lshw/wifi_disp/wifi_disp/proc3.h

#ifndef __PROC3_H__
#define __PROC3_H__
//发送温度湿度压力到tcp服务器
void proc3_setup() {
  WiFiUDP udp;
  String msg;
  if (nvram.proc3_host[0] == 0)
    return;
  set_hostname();
  if (nvram.have_dht) {
    if (wendu < -299.0)
      dht_();
    wifi_set_opmode(STATION_MODE);
    wifi_station_connect();
  }
  _myTicker.attach(1, timer1s);
  wait_connected(10000);
  nvram.charge = 1;  //充电
  nvram.change = 1;
  save_nvram();
  if (nvram.have_dht) {
    if (wendu < -299.0) {
      if (!dht_()) poweroff(1);
    }
  }
  get_value();
  fix_proc3_set();
  shan();
  Serial.flush();
  if (WiFi_isConnected()) {
    delay(100);
    msg = val_str();
    udp.begin(nvram.proc3_port);
    if (udp.beginPacket(nvram.proc3_host, nvram.proc3_port)
        || udp.beginPacket(nvram.proc3_host, nvram.proc3_port)
        || udp.beginPacket(nvram.proc3_host, nvram.proc3_port)) {
      if (udp.println(msg)
          || udp.println(msg)
          || udp.println(msg)) {
        udp.endPacket();
        Serial.println(F("send ok"));
      }
    }
    Serial.printf_P(PSTR("to %s:%d [%s]\r\n"), nvram.proc3_host, nvram.proc3_port, msg.c_str());
    Serial.flush();
  }
  delay(100);
  poweroff(nvram.proc3_sec);
}
#endif  //__PROC3_H__
