lshw/wifi_disp/wifi_disp/dht22.h

#ifndef __DHT_H__
#define __DHT_H__

extern float wendu, shidu;
uint8_t temp_data[6];
uint32_t dht_next = 600;
#define DHT_PIN 0
bool dht() {
  uint8_t p1, dat[40];
  // empty output data.
  pinMode(DHT_PIN, INPUT_PULLUP);
  if (dht_next > millis()) {
    if (dht_next > millis() + 600)
      dht_next = millis() + 600;
    Serial.printf_P(PSTR("delay(%ld)\r\n"), dht_next - millis());
    while (dht_next > millis()) {
      delay(100);
      yield();
    }
  }
  dht_next = millis() + 600;

  // According to protocol: http://akizukidenshi.com/download/ds/aosong/AM2302.pdf
  // notify DHT22 to start:
  //    1. T(be), PULL LOW 1ms(0.8-20ms).
  //    2. T(go), PULL HIGH 30us(20-200us), use 40us.
  //    3. SET TO INPUT or INPUT_PULLUP.
  pinMode(DHT_PIN, OUTPUT);
  digitalWrite(DHT_PIN, LOW);
  cli();
  delayMicroseconds(20000);
  // Pull high and set to input, before wait 40us.
  // @see https://github.com/winlinvip/SimpleDHT/issues/4
  // @see https://github.com/winlinvip/SimpleDHT/pull/5
  digitalWrite(DHT_PIN, HIGH);
  pinMode(DHT_PIN, INPUT_PULLUP);
  delayMicroseconds(40);

  // DHT22 starting:
  //    1. T(rel), PULL LOW 80us(75-85us).
  //    2. T(reh), PULL HIGH 80us(75-85us).
  //levelTime(pin, LOW);
  //levelTime(pin, HIGH);
  p1 = pulseIn(DHT_PIN, HIGH, 200);
  if (p1 > 120) {
    sei();
    return false;
  }
  // DHT22 data transmite:
  //    1. T(LOW), 1bit start, PULL LOW 50us(48-55us).
  //    2. T(H0), PULL HIGH 26us(22-30us), bit(0)
  //    3. T(H1), PULL HIGH 70us(68-75us), bit(1)
  for (int j = 0; j < 40; j++) {
    dat[j] = pulseIn(DHT_PIN, HIGH, 200);
  }
  sei();
  for (int j = 0; j < 40; j++) {
    temp_data[j / 8] = (temp_data[j / 8] << 1) | (dat[j] > 40 ? 1 : 0);  // specs: 22-30us -> 0, 70us -> 1
  }
  Serial.printf_P(PSTR("start=%d, %02x%02x %02x%02x %02x\r\n"), p1,
                  temp_data[0],
                  temp_data[1],
                  temp_data[2],
                  temp_data[3],
                  temp_data[4]);
  for (int j = 0; j < 40; j++) {
    Serial.printf_P(PSTR(" %02d"), dat[j]);
    if (j % 8 == 7)
      Serial.println();
  }
  if (
    ((temp_data[0] + temp_data[1] + temp_data[2] + temp_data[3]) & 0xff) == temp_data[4]
    && ((temp_data[0] + temp_data[1] + temp_data[2] + temp_data[3] + temp_data[4]) != 0)) {
    wendu = 0.1 * ((temp_data[2] & 0x7f) << 8 | temp_data[3]);
    shidu = 0.1 * (temp_data[0] << 8 | temp_data[1]);
    if ((temp_data[2] & 0x80) != 0)
      wendu = -wendu;
    Serial.printf_P(PSTR("millis()=%ld, 温度=%.1f, 湿度=%.1f%%\r\n"), millis(), wendu, shidu);
    return true;
  } else {
    wendu = -999.0;
    shidu = -999.0;
    Serial.println(F("数据校验错"));
    return false;
  }
}
bool dht_() {
  if (!dht() && !dht() && !dht())
    return dht();
  return true;
}
#endif
