lshw/wifi_disp/wifi_disp/proc4.h

#ifndef __PROC4_H__
#define __PROC4_H__
//lora转发到internet  通过wifi
uint16_t send_limit = 0;
void limit_speed() {  //令牌桶算法，限制转发的速率
  if (send_limit > 0) send_limit--;
}
void proc4_setup() {
  init1();
  if (power_in) {
    _myTicker.attach(1, limit_speed);
    Serial.println(F("lora 网关模式"));
    disp(F("P4-L "));
    wifi_set_opmode(STATION_MODE);
    wifi_station_connect();
    set_hostname();
    hello();
    if (!wait_connected(30000)) {
      poweroff(10);
    }

  } else {
    Serial.println(F("lora 远端模式"));
    disp(F("P4-S "));
    lora_send_wendu();
    delay(100);
    poweroff(nvram.proc3_sec);
  }
}
#endif  //__PROC4_H__
