lshw/wifi_disp/lora_mini/lora.h

#include <SPI.h>
#include "sx1278.h"
#define DIO0 2
#define DIO1 3
#define DIO2 A0
#define NSS_PIN  10
#define RESET_PIN  9
#define LORA_VCC 8
LoRa lora;
extern float temp, bat_v;
extern byte dsn[8];
uint8_t len;
char buf[256];
uint16_t lora_count = 0;
uint32_t ms;
void lora_tx_int() {
  //digitalWrite(13,LOW);
//  Serial.begin(9600);
//  Serial.println(millis() - ms);
//  Serial.flush();
  min_dog = 0;//清看门狗
}
void lora_send_loop() {
  lora_count++;
  String str;
  pinMode(DIO0, INPUT);
  digitalWrite(DIO0, LOW);
  lora.enterTxMode();
  lora.setTxInterrupt();	// enable RxDoneIrq
  sprintf(buf, "S%04d,%02x%02x%02x%02x%02x%02x%02x%02x,", lora_count % 10000, dsn[0], dsn[1], dsn[2], dsn[3], dsn[4], dsn[5], dsn[6], dsn[7], temp, (int)(bat_v * 1000));
  str = String(temp);
  strcat(buf, String(temp).c_str());
  strcat(buf, ",");
  strcat(buf, String(bat_v).c_str());
  Serial.println(buf);
  //disp(disp_buf);
  //digitalWrite(13,HIGH);
  lora.sendPackage((uint8_t *)buf, strlen(buf)); // sending data
  attachInterrupt(0, lora_tx_int, HIGH);
  wdt_reset(); //让wdt中断，1秒后发生，防止wdt中断，干扰lora发送完成中断
  ms = millis();
  power_down();//cpu掉电模式， 等待发送完成
  detachInterrupt(0);
  lora.clearIRQFlags();
  lora.sleep();//发送完成，lora休眠
}
uint8_t lora_rxtx = 0; //1:rx 2:tx
void lora_receive_loop() {
  if (lora_rxtx != 1) {
    lora.rxInit();
    lora_rxtx = 1;
  }
  if (lora.waitIrq()) {
    lora.clearIRQFlags();
    len = lora.receivePackage(buf);
    Serial.write(buf, len);
    Serial.println();
    buf[0] = 'L';
    //    disp((char *)rxBuf);
    lora.rxInit();

    Serial.print("with RSSI ");
    uint8_t rssi = 137 - lora.readRSSI(1); //-dBm
    Serial.println(rssi);
  }
}
bool lora_state = false;
void lora_init() {
  //  if (lora_state && digitalRead(LORA_VCC) == LOW) return;
  //  digitalWrite(LORA_VCC, LOW);
  //  delay(1);
  lora_state = lora.init(10, 9);
  lora.idle();    // turn to standby mode
  //lora.sleep();
  lora.setFrequency(434500000); //434.5Mhz
  lora.setRFpara(LR_BW_250k, LR_CODINGRATE_2, 12, LR_PAYLOAD_CRC_ON); //BW带宽,CR编码率,SF扩频因子，CRC
  // preamble length is 6~65535
  lora.setPreambleLen(12);//前导60
  //lora.setPayloadLength(10); //数据长度10
  //lora.setTxPower(15); //default set 20db
  // mode LR_IMPLICIT_HEADER_MODE or LR_EXPLICIT_HEADER_MODE
  lora.setHeaderMode(LR_EXPLICIT_HEADER_MODE);//不要header
}
